mavory/Smart-alarm-clock/Circuit diagram/ESP32.kicad_sch

## KiCad design Circuit diagram/ESP32.kicad_sch (2026-01-17)

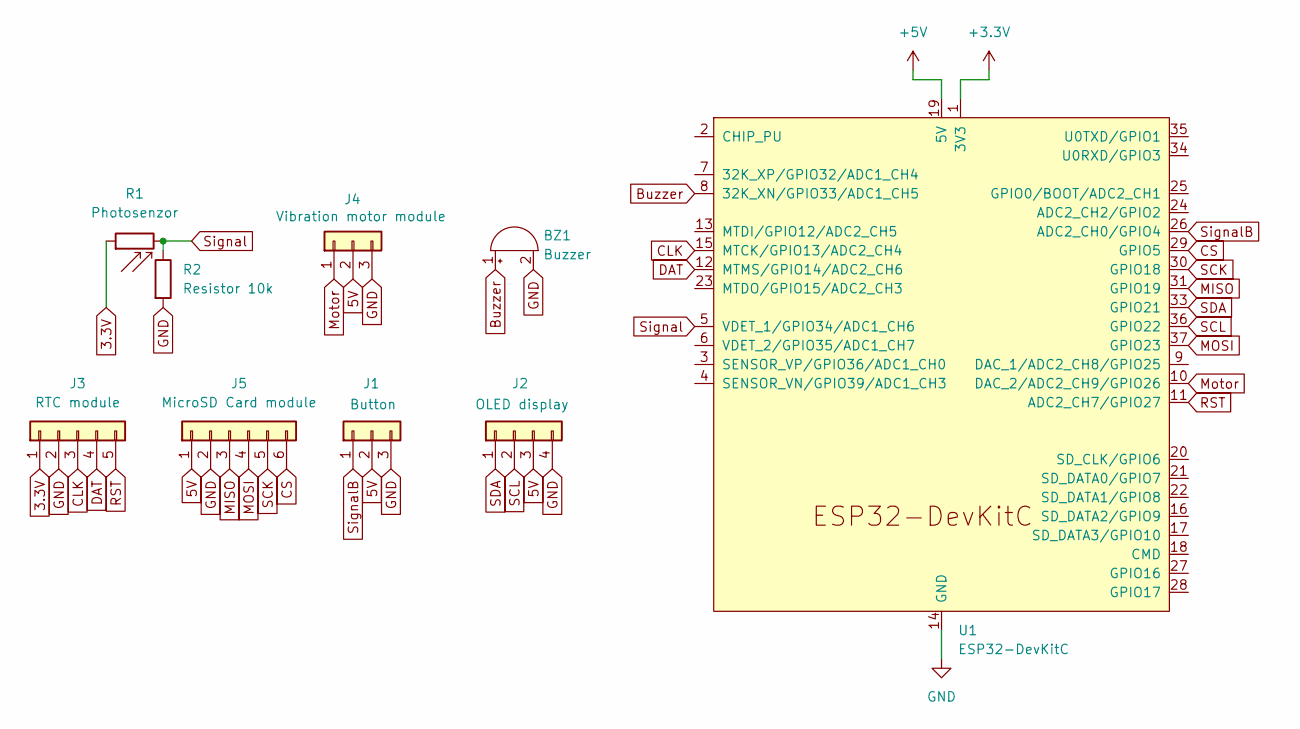
[picture p17: schematic ESP32.kicad_sch]

Parts:
BZ1: Buzzer
J1: Button
J2: OLED display
J3: RTC module
J4: Vibration motor module
J5: MicroSD Card module
R1: Photosenzor; R_LDR_5.1x4.3mm_P3.4mm_Vertical
R2: Resistor 10k
U1: ESP32-DevKitC

Connections:
3.3V: J3.1, R1.1
5V: J1.2, J2.3, J4.2, J5.1
+3.3V: U1.1 (3V3)
+5V: U1.19 (5V)
Buzzer: BZ1.1 (+), U1.8 (32K_XN/GPIO33/ADC1_CH5)
CLK: J3.3, U1.15 (MTCK/GPIO13/ADC2_CH4)
CS: J5.6, U1.29 (GPIO5)
DAT: J3.4, U1.12 (MTMS/GPIO14/ADC2_CH6)
GND: BZ1.2 (-), J1.3, J2.4, J3.2, J4.3, J5.2, R2.2, U1.14 (GND), U1.32 (GND), U1.38 (GND)
MISO: J5.3, U1.31 (GPIO19)
MOSI: J5.4, U1.37 (GPIO23)
Motor: J4.1, U1.10 (DAC_2/ADC2_CH9/GPIO26)
RST: J3.5, U1.11 (ADC2_CH7/GPIO27)
SCK: J5.5, U1.30 (GPIO18)
SCL: J2.2, U1.36 (GPIO22)
SDA: J2.1, U1.33 (GPIO21)
Signal: R1.2, R2.1, U1.5 (VDET_1/GPIO34/ADC1_CH6)
SignalB: J1.1, U1.26 (ADC2_CH0/GPIO4)
