mavory/Smart-alarm-clock/Photos/20260110_124549.jpg

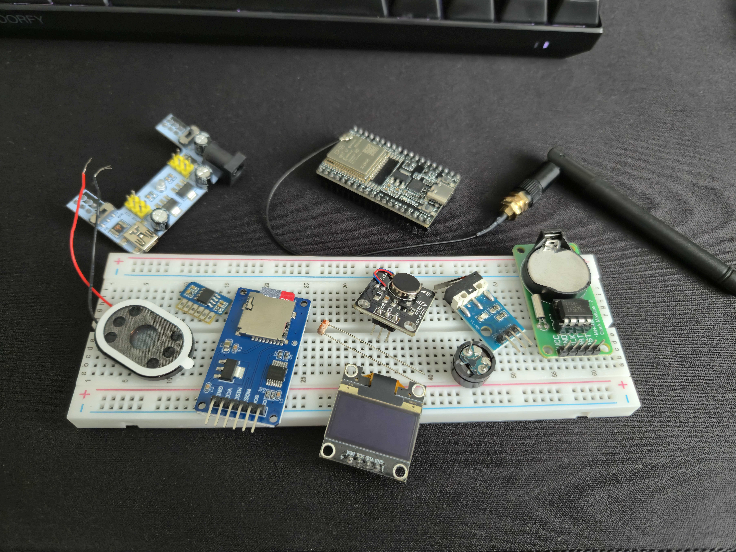
Photos/20260110_124549.jpg
