mavory/Smart-alarm-clock/Photos/20260110_181154.jpg

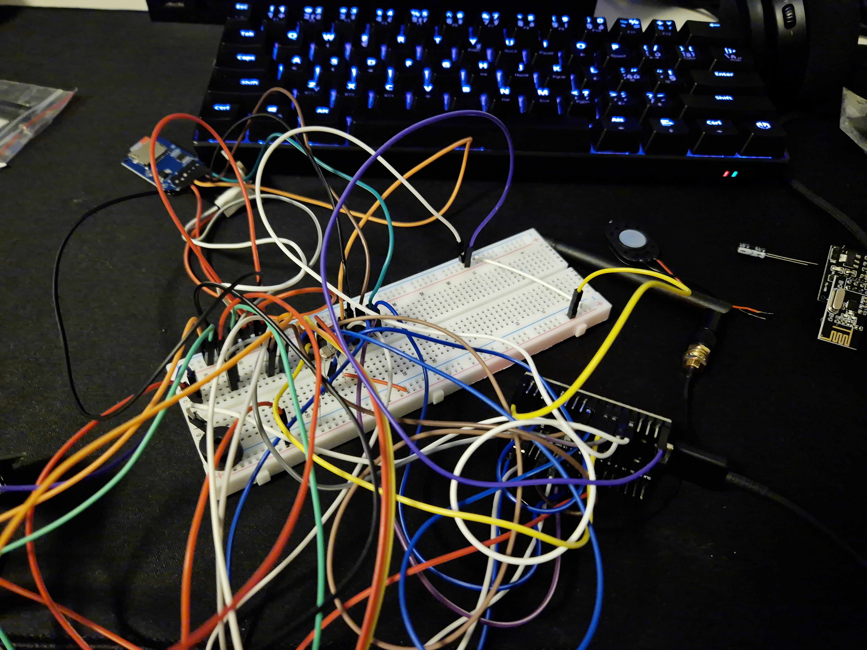
Photos/20260110_181154.jpg
