mavory/Smart-alarm-clock/Photos/20260110_181206.jpg

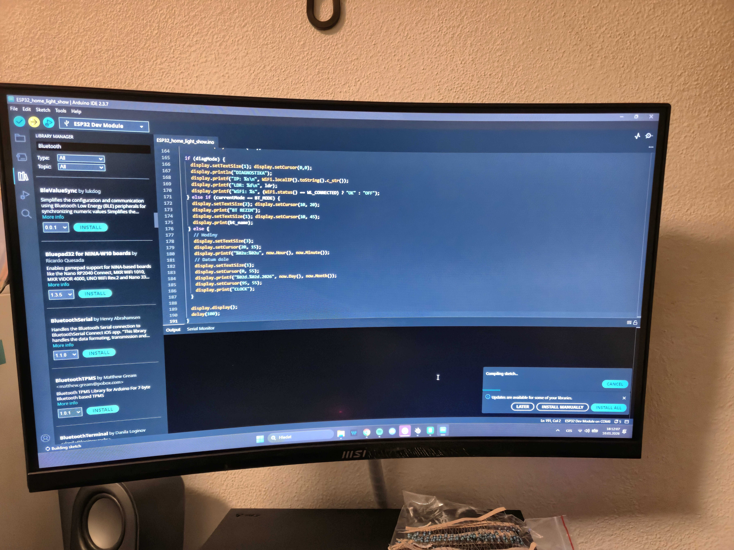
Photos/20260110_181206.jpg
