mavory/Smart-alarm-clock/Photos/20260110_190623.jpg

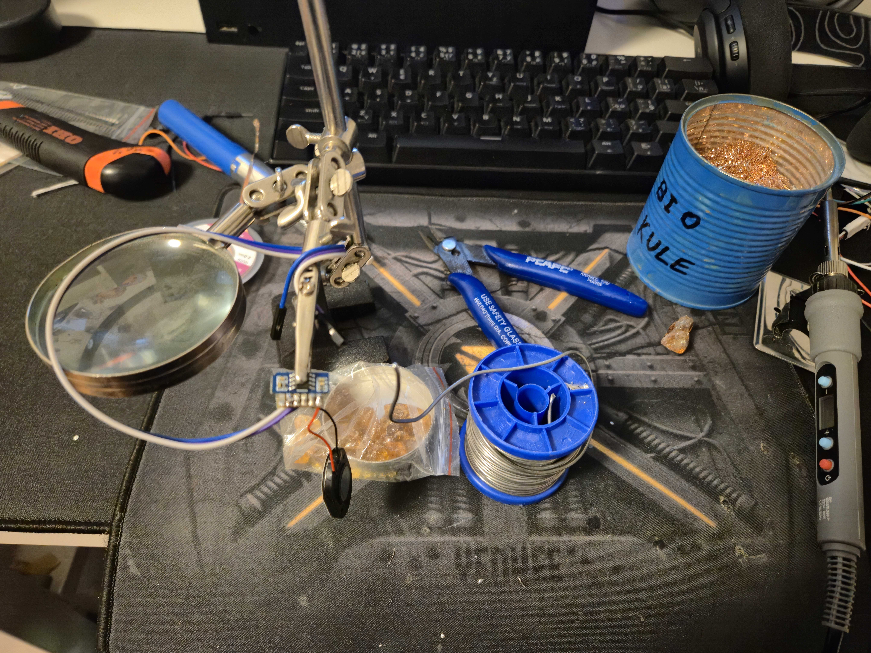
Photos/20260110_190623.jpg
