mavory/Smart-alarm-clock/Photos/20260111_003507.jpg

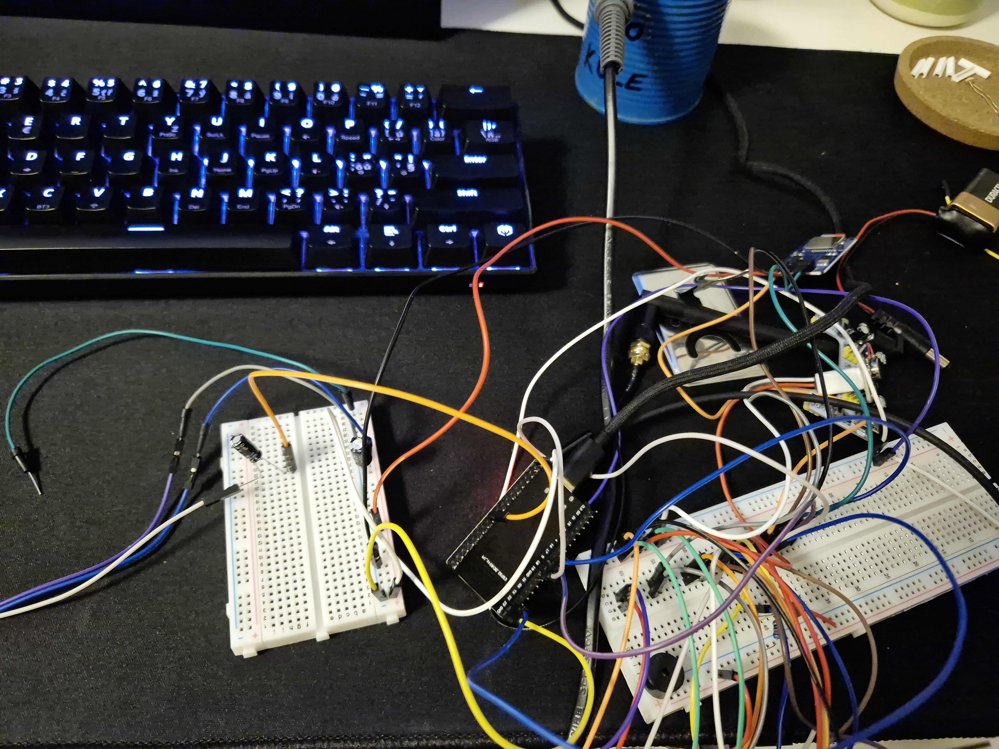
Photos/20260111_003507.jpg
