mavory/Smart-alarm-clock/Photos/20260111_123509.jpg

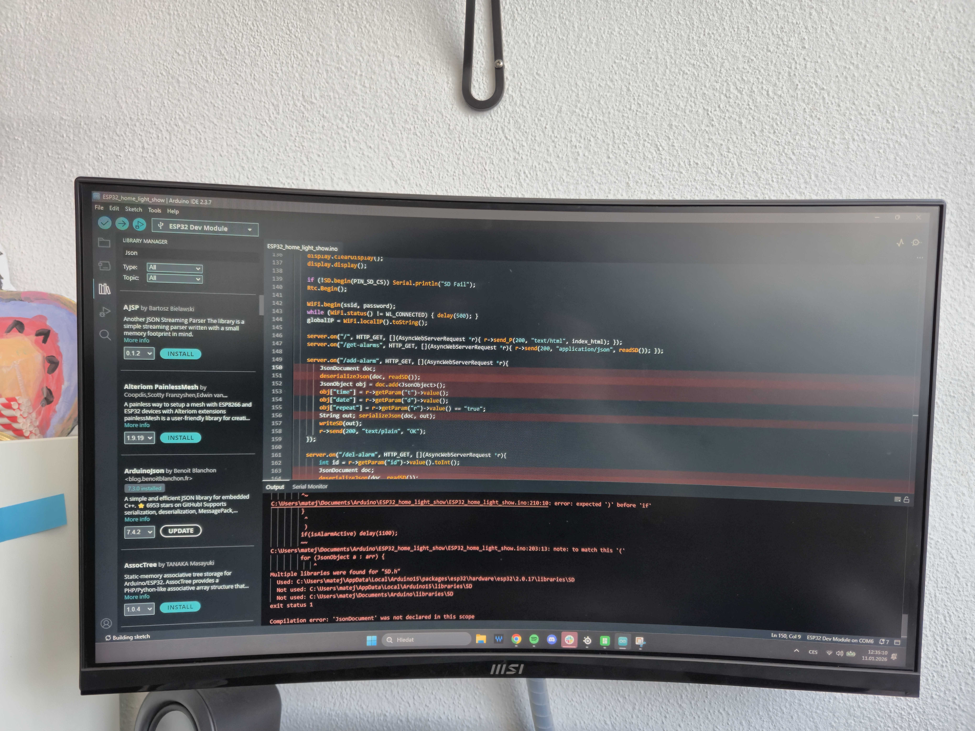
Photos/20260111_123509.jpg
