mavory/Smart-alarm-clock/Photos/20260112_203034.jpg

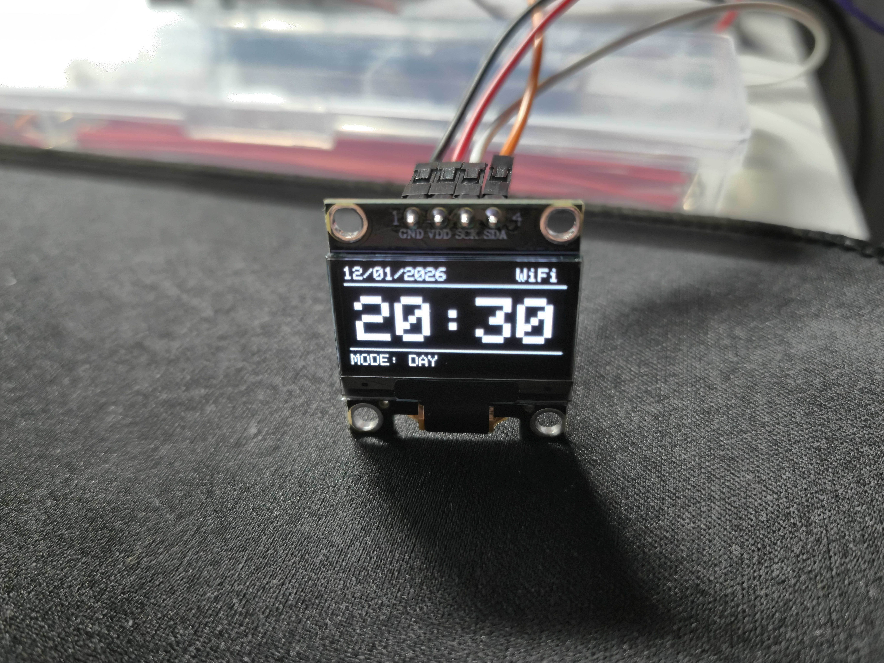
Photos/20260112_203034.jpg
