mavory/Smart-alarm-clock/Photos/20260112_203047.jpg

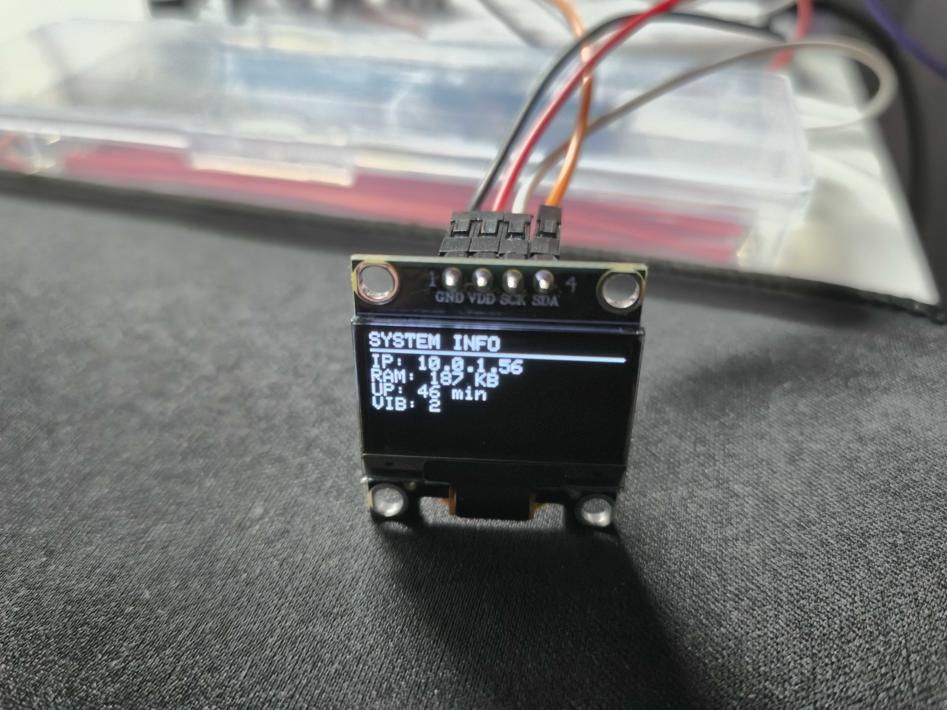
Photos/20260112_203047.jpg
