mavory/Smart-alarm-clock/Photos/20260116_191652.jpg

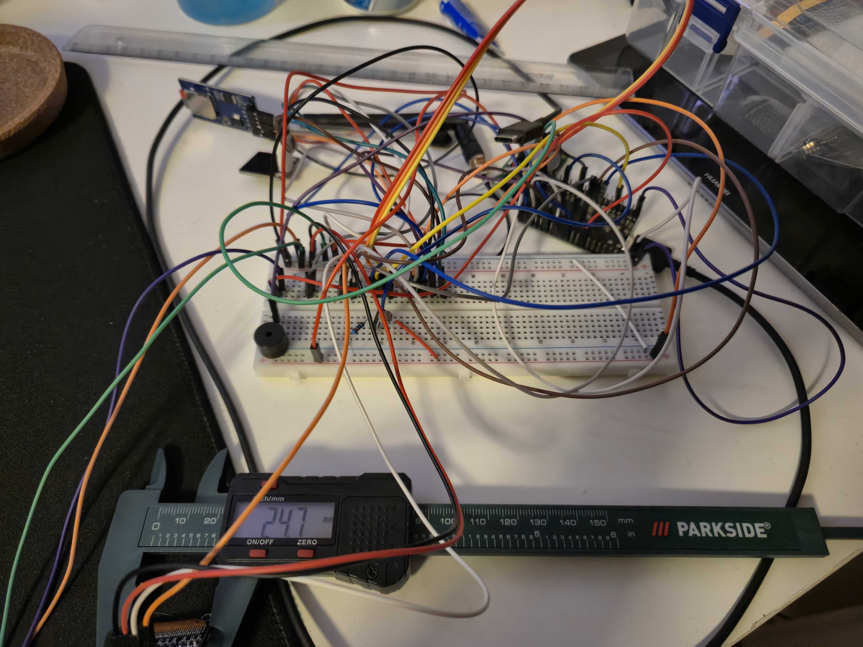
Photos/20260116_191652.jpg
