mavory/Smart-alarm-clock/Photos/20260116_224936 (2).jpg

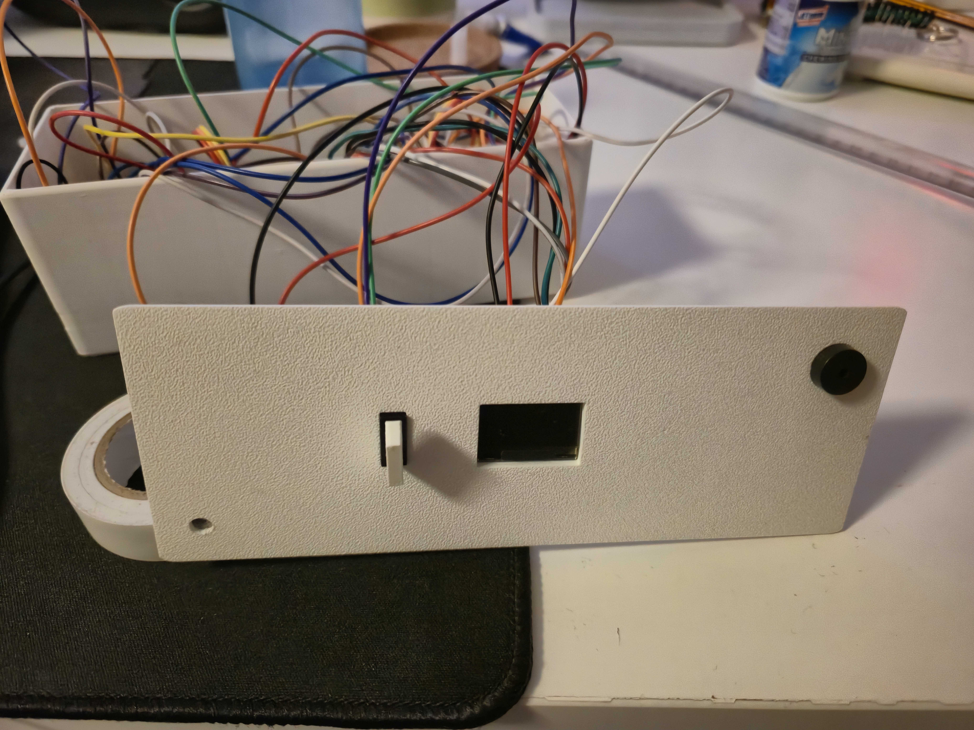
Photos/20260116_224936 (2).jpg
