mavory/Smart-alarm-clock/Photos/20260116_232352.jpg

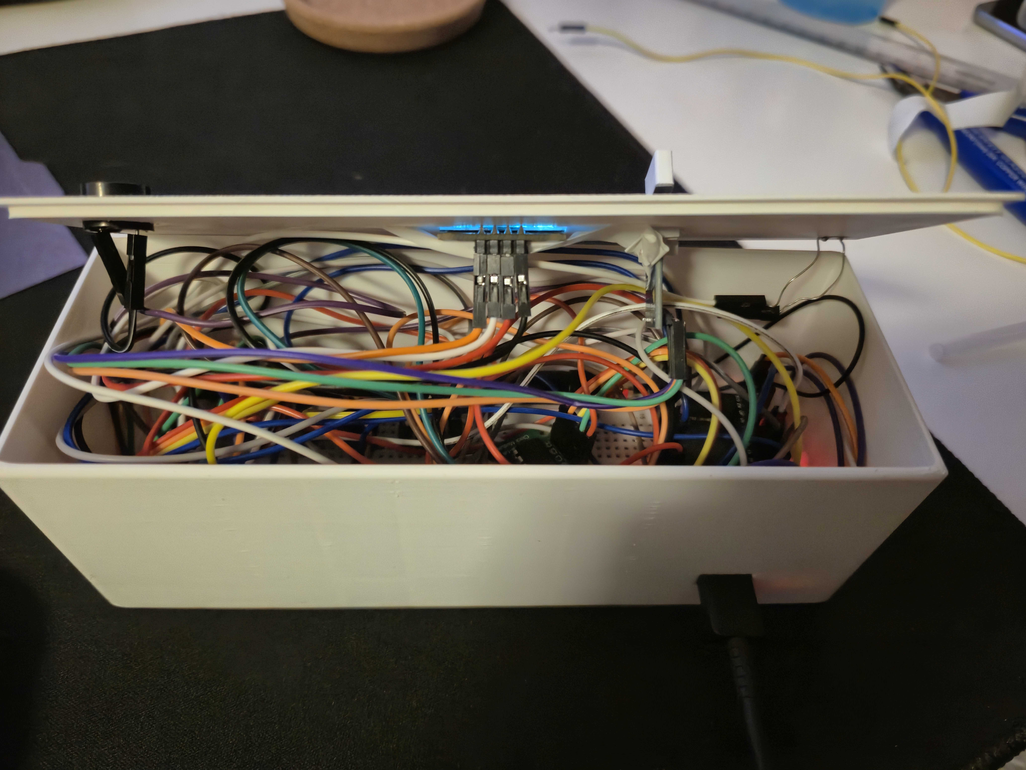
Photos/20260116_232352.jpg
