mavory/Smart-alarm-clock/Photos/20260116_232608.jpg

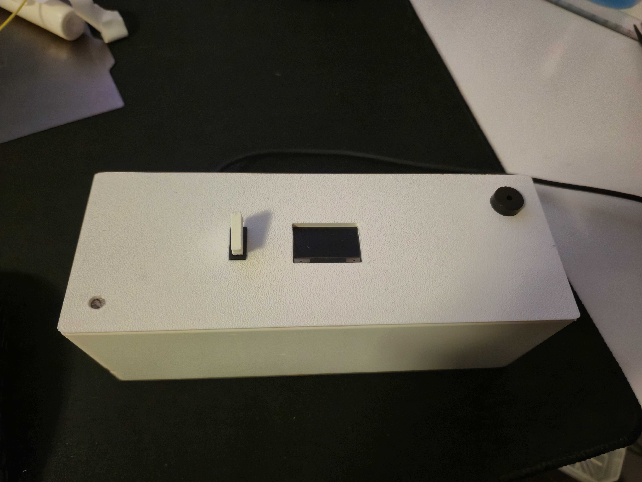
Photos/20260116_232608.jpg
